Jake-Eshelman-Portfolio/Smart_Garden/Core/Src/timer_module.c

/*
 * timer_module.c
 *
 *  Created on: Aug 5, 2024
 *      Author: jakee
 */

#include "timer_module.h"
#include "FreeRTOS.h"
#include "task.h"
#include "timers.h"
#include "stm32f4xx_hal.h"
#include "stm32f4xx_hal_rtc.h"
#include "stm32f4xx_hal_pwr.h"
#include "stm32f4xx_hal_rcc.h"
